jonbro/aleatorium/Firmware/GrooveBox.h

#ifndef GROOVEBOX_H_
#define GROOVEBOX_H_

#include <stdio.h>
#include "pico/stdlib.h"
#include "pico/time.h"
#include "pico/rand.h"

#include "Instrument.h"
extern "C" {
  #include "ssd1306.h"
}
#include "q15.h"
#include "Midi.h"
#include "hardware.h"
#include "voice_data.h"
#include "SongData.h"
#include "audio/resources.h"
#include "Reverb2.h"
#include "Delay.h"
#include "MidiParamMapper.h"
#include "GlobalData.pb.h"
#include "USBSerialDevice.h"
#include "lua.hpp"

#define VOICE_COUNT 8

class GrooveBox {
 public:
  void init(uint32_t *_color, lua_State *L);
  void OnAdcUpdate(uint16_t a);
  void SetGlobalParameter(uint8_t a, uint8_t b, bool setA, bool setB);
  bool IsPlaying();
  int GetNote();
  int GetNoteMidi();
  void Render(int16_t* output_buffer, int16_t* input_buffer, size_t size);
  uint8_t GetInstrumentParamA(int voice);
  uint8_t GetInstrumentParamB(int voice);
  void OnFinishRecording();
  Instrument instruments[VOICE_COUNT];
  int CurrentStep = 0;
  uint8_t currentVoice = 0;
  bool recording = false;
  uint32_t recordingLength;
  bool erasing = false;
  bool playThroughEnabled = false;
  uint8_t GetCurrentPattern()
  {
    return playingPattern;//patternChain[chainStep];
  }

  void ResetADCLatch()
  {
    paramSetA = paramSetB = false;
  }

  void ResetPatternOffset()
  {
    for (size_t i = 0; i < 17; i++)
    {
        patternStep[i] = 0;
        beatCounter[i] = 0;
        if(i<16)
          patternLoopCount[i] = 0;
    }
    beatCounter[17] = 0;
  }
  void OnCCChanged(uint8_t cc, uint8_t newValue);
  static int getTickCountForRateIndex(int rate)
  {
    switch(rate)
    {
      case 0: // 2x
        return 12;
      case 1: // 3/2x
        return 16;
        break;
      case 2: // 1x
        return 24;
        break;
      case 3: // 3/4x
        return 32;
        break;
      case 4: // 1/2x
        return 48;
        break;
      case 5: // 1/4x
        return 96;
        break;
      case 6: // 1/8x
        return 192;
        break;
      case 7: // 24ppq
        return 4;
    }
    return 24;
  }
  VoiceData patterns[16];
  void StartPlaying();
  int syncsRequired = 0;
  uint8_t globalVolume = 0x0;

 private:
  lua_State *L;
  void SaveAndShutdown();
  USBSerialDevice *usbSerialDevice;
  MidiParamMapper midiMap;
  int8_t needsInitialADC = 30; 
  void SerializeToSerial();
  void DeserializeFromSerial();
  void TriggerInstrument(uint8_t key, int16_t midi_note, uint8_t step, uint8_t pattern, bool livePlay, VoiceData &voiceData, int channel);
  void TriggerInstrumentMidi(int16_t midi_note, uint8_t step, uint8_t pattern, VoiceData &voiceData, int channel);
  void CalculateTempoIncrement();
  void OnTempoPulse();
  uint8_t voiceCounter = 0;
  uint8_t instrumentParamA[8];
  uint8_t instrumentParamB[8];
  int needsNoteTrigger = -1;
  int drawY = 0;
  uint16_t drawCount = 0;
  int lastNotePlayed = 60;
  uint8_t lastKeyPlayed = 0;
  bool paramSetA, paramSetB;
  uint32_t tempoPhaseIncrement = 0, tempoPhase = 0;
  uint8_t beatCounter[20] = {0};
  bool playing = false;
  bool waitingForSync = false;
  bool writing = false;
  bool holdingWrite = false;
  bool holdingEscape = false;
  bool holdingMute = false;
  bool holdingArm = false;
  uint8_t recordingTarget = 0;
  int clearTime = -1;
  int shutdownTime = -1;
  int powerHoldTime = -1;
  bool liveWrite = false;
  bool soundSelectMode = false;
  bool patternSelectMode = false;
  bool paramSelectMode = false;
  
  // used for midi learn mode
  int16_t lastEditedParam = -1;
  
  bool selectedGlobalParam = false;
  uint8_t param = 5;
  uint32_t *color;
  uint16_t hadTrigger = 0;
  // defaults to allow all playback
  uint16_t allowPlayback = 0xffff;
  // each sound can be on a different step through the pattern, we should track these
  uint8_t patternStep[17] = {0};

  // for tracking how many times we've looped through a pattern
  uint8_t patternLoopCount[16] = {0};

  uint32_t framesSinceLastTouch = 0;
  // the page we are currently editing for each sound
  // clamped to the length of this pattern / sound
  uint8_t editPage[16] = {0};
  uint8_t playingPattern = 0;
  int patternChain[16] = {0};
  int8_t voiceChannel[16] = {-1};
  
  int patternChainLength = 1;
  int chainStep = 0;
  bool nextPatternSelected = false;
  uint8_t storingParamLockForStep = 0;
  bool parameterLocked;
  VoiceData *Editing;
  VoiceData *Playing;
  SongData songData;
  Midi midi;
  uint16_t nextTrigger = 0;
  uint8_t lastAdcValA = 0;
  uint8_t lastAdcValB = 0;
  uint16_t AdcInterpolatedA = 0;
  uint16_t AdcInterpolatedB = 0;
  Delay delay;
  Reverb2 verb;
  int64_t renderTime = 0;
  int64_t sampleCount = 0;
  GlobalData globalData = GlobalData_init_zero;
};

extern GrooveBox *groovebox; // used for the midi callbacks

#endif // GROOVEBOX_H_
