jonbro/aleatorium/Firmware/Midi.cc

#include "Midi.h"
#include "hardware/irq.h"
#include "hardware/dma.h"
#include <stdio.h>
#include <string.h>
#include "tusb.h"

#define UART_ID uart1
#define BAUD_RATE 31250
#define UART_TX_PIN 4
#define UART_RX_PIN 5

static int chars_rxed = 0;
uint8_t in_buf[128];
uint8_t buf_count = 0;
bool readBuf = false;
void on_uart_rx() {
    while (uart_is_readable(UART_ID)) {
        char c = uart_getc(UART_ID);
        in_buf[buf_count++] = c;
        readBuf = false;
    }
}

void Midi::Init()
{
    // clear out the last values so we immediately update on first get
    for(int i=0;i<128;i++)
    {
        lastCCValue[i] = 0xff;
    }
    // Set up our UART with the required speed.
    uart_init(UART_ID, BAUD_RATE);

    // Set the TX and RX pins by using the function select on the GPIO
    // Set datasheet for more information on function select
    gpio_set_function(UART_TX_PIN, GPIO_FUNC_UART);
    gpio_set_function(UART_RX_PIN, GPIO_FUNC_UART);

    int UART_IRQ = UART_ID == uart0 ? UART0_IRQ : UART1_IRQ;
    irq_set_exclusive_handler(UART_IRQ, on_uart_rx);
    irq_set_enabled(UART_IRQ, true);

    // Now enable the UART to send interrupts - RX only
    uart_set_irq_enables(UART_ID, true, false);
    TxIndex = 0;
    //
    DmaChannelTX = dma_claim_unused_channel(true);

    dma_channel_config txConfig = dma_channel_get_default_config(DmaChannelTX);
    channel_config_set_transfer_data_size(&txConfig, DMA_SIZE_8);
    channel_config_set_read_increment(&txConfig, true);
    channel_config_set_write_increment(&txConfig, false);
    channel_config_set_ring(&txConfig, false, MIDI_BUF_LENGTH_POW);
    channel_config_set_dreq(&txConfig, DREQ_UART1_TX);
    dma_channel_set_config(DmaChannelTX, &txConfig, false);
    dma_channel_set_write_addr(DmaChannelTX, &uart1_hw->dr, false);
    initialized = true;
}

uint16_t Midi::Write(const uint8_t* data, uint16_t length)
{
}

void Midi::Flush()
{
    if(!initialized || dma_channel_is_busy(DmaChannelTX))
        return;
    // Size check
    if (TxIndex == 0)
    {
        return;
    }
    uint8_t* start = &TxBuffer[MIDI_BUF_LENGTH*pingPong];
    dma_channel_transfer_from_buffer_now(DmaChannelTX, start, TxIndex);
    pingPong = (pingPong+1)%2;
    TxIndex = 0;
}

int Midi::GetNote()
{
    if(readBuf)
        return -1;

    uint8_t cmdStart = 0;
    // filter out all non 0x9 commands
    while(((in_buf[cmdStart]>>4) != 0x9 && (in_buf[cmdStart]>>4) != 0xb) && cmdStart<buf_count)
    {
        cmdStart++;
        while((in_buf[cmdStart]>>7) != 1 && cmdStart<buf_count)
        {
            cmdStart++;
        }
    }
    if(cmdStart>buf_count)
    {
        buf_count = 0;
        return -1;
    }
    if((in_buf[cmdStart]>>4) == 0x9)
    {
        readBuf = true;
        buf_count = 0;
        return in_buf[cmdStart+1]&0x7f; // midi data bytes strip off the top bit
    }
    // control change
    if((in_buf[cmdStart]>>4) == 0xb)
    {
        uint8_t cc = in_buf[cmdStart+1];
        uint8_t val = in_buf[cmdStart+2];
        if(lastCCValue[cc] == 0xff || lastCCValue[cc] != val)
        {
            if(OnCCChanged != NULL)
            {
                OnCCChanged(cc, val);
            }
            lastCCValue[cc] = val;
        }
        //printf("cc: %i %i\n",in_buf[cmdStart+1], in_buf[cmdStart+2]);
        buf_count = 0;
        return -1;
    }
    // note off
    buf_count = 0;
    return -1;
}
void Midi::NoteOn(uint8_t channel, uint8_t pitch, uint8_t velocity)
{
    uint8_t send[] = {0x90+channel,pitch,velocity};
    Write(send, 3);
}

void Midi::NoteOff(uint8_t channel, uint8_t pitch)
{
    uint8_t send[] = {0x90+channel,pitch,0};
    Write(send, 3);
}

void Midi::StartSequence()
{
    uint8_t sendValue = 0xFA;
    Write(&sendValue, 1);
}
void Midi::StopSequence()
{
    uint8_t sendValue = 0xFC;
    Write(&sendValue, 1);
}
void Midi::TimingClock()
{
    uint8_t sendValue = 0xF8;
    Write(&sendValue, 1);
}
