jonbro/aleatorium/Firmware/AudioSampleSecondbloop.cpp

// Audio data converted from WAV file by wav2sketch

#include "AudioSampleSecondbloop.h"

// Converted from secondbloop.wav, using 44100 Hz, 16 bit PCM encoding
const unsigned int AudioSampleSecondbloop[16065] = {
0x81007D03,0x089B006F,0x1A1111C8,0x2AB322D2,0x3A0D32D2,0x47A8414E,0x531F4DDA,0x5C195811,
0x62545FAA,0x65A0646B,0x65E7662A,0x632164E3,0x5D69609B,0x54EA5975,0x49E44FA2,0x3CA84379,
0x2DA1354F,0x1D44258D,0x0C0914AE,0xFA710336,0xE906F1AA,0xD84DE08C,0xC8C3D061,0xBAE6C1A0,
0xAF19B4BB,0xA5B4AA14,0x9F01A1FF,0x9B2C9CBC,0x9A599A6E,0x9C959B25,0xA1C59ED3,0xA9C0A56D,
0xB447AEB9,0xC113BA6F,0xCFBAC835,0xDFD3D7A2,0xF0DDE83E,0x0256F990,0x13BB0B14,0x248A1C3C,
0x343C2C8D,0x425B3B90,0x4E8748C2,0x586153C5,0x5F905C46,0x63E3620E,0x653964EF,0x639364CA,
0x5EFA619E,0x57845B91,0x4D7752CB,0x411F4790,0x32D83A31,0x230F2B1B,0x123D1ABD,0x00E40996,
0xEF87F826,0xDEAAE6F3,0xCEC8D685,0xC05EC757,0xB3DDB9DE,0xA9A3AE76,0xA201A57E,0x9D2C9F35,
0x9B459BD0,0x9C599B6D,0xA0639E0C,0xA74FA390,0xB0E2ABCC,0xBCCAB688,0xCAAAC37A,0xDA1FD23B,
0xEAB4E256,0xFBEDF34D,0x0D4504A0,0x1E3315CE,0x2E382655,0x3CD735B8,0x49A74381,0x54454F43,
0x5C6158A6,0x61BC5F64,0x6429634C,0x639D6440,0x60196237,0x59B75D43,0x50AC558B,0x453F4B42,
0x37C33EBD,0x289D305E,0x18462091,0x07380FC9,0xF5F5FE90,0xE4FBED64,0xD4D5DCCB,0xC5FECD3B,
0xB8E1BF2E,0xADDDB319,0xA553A94D,0x9F81A211,0x9C8B9DA4,0x9C899C27,0x9F7C9DA5,0xA54FA212,
0xADD9A945,0xB8D1B30C,0xC5E5BF1F,0xD4B3CD1E,0xE4CBDC9E,0xF5AFED29,0x06DCFE43,0x17D30F6B,
0x28162019,0x37232FCD,0x448A3E16,0x4FE64A84,0x58DF54B6,0x5F335C62,0x62AE614E,0x633C6352,
0x60D46262,0x5B895E83,0x538657D7,0x49064E8E,0x3C5B42F1,0x2DEB3553,0x1E1C2621,0x0D6815CF,
0xFC4C04DE,0xEB50F3CA,0xDAF6E314,0xCBBED33A,0xBE19C4B0,0xB269B7ED,0xA902AD58,0xA236A53D,
0x9E369FD2,0x9D1A9D4B,0x9EF29DB5,0xA3B6A107,0xAB38A726,0xB53DAFED,0xC177BB18,0xCF8BC84E,
0xDF0ED731,0xEF91E740,0x008EF808,0x117E090F,0x21E819D3,0x315329C9,0x3F403880,0x4B474588,
0x5512507E,0x5C545909,0x60D75EEC,0x627361FC,0x61196227,0x5CE05F69,0x55E959CF,0x4C695181,
0x40A346C7,0x32EC39F8,0x23AF2B74,0x136C1BA7,0x02950B03,0xF1A9FA12,0xE129E956,0xD1A0D943,
0xC378CA57,0xB71FBD06,0xACF4B1B7,0xA543A8BB,0xA045A25C,0x9E1D9ECA,0x9EE09E1F,0xA290A05A,
0xA901A569,0xB200AD35,0xBD55B779,0xCAB1C3D8,0xD99ED1FC,0xE9A3E185,0xFA56F1F8,0x0B3402CD,
0x1BB6138D,0x2B6323B8,0x39C732CE,0x466F405E,0x50FE4C01,0x59215560,0x5E9B5C35,0x61416049,
0x61066182,0x5DE65FCE,0x57F65B46,0x4F6A5409,0x44894A47,0x37A03E4C,0x2908307C,0x193D2140,
0x08B71106,0xF7EE0048,0xE762EF91,0xD795DF5B,0xC904D019,0xBC16C245,0xB12AB64E,0xA897AC8E,
0xA2A0A54A,0x9F74A0BA,0x9F2A9EFD,0xA1C7A021,0xA72FA41E,0xAF36AAD9,0xB9A5B422,0xC627BFA9,
0xD464CD1B,0xE3EBDC0D,0xF44DEC0A,0x0500FC9E,0x15890D4D,0x256D1D94,0x34362CF6,0x416B3AFC,
0x4CA74746,0x559C5170,0x5C095927,0x5FB45E34,0x60846076,0x5E705FDB,0x59935C66,0x520F562A,
0x48164D5F,0x3BFA424D,0x2E18353F,0x1ED8269D,0x0EAD16D9,0xFE13066A,0xED8BF5CD,0xDD94E57E,
0xCEA7D5FA,0xC132C7B7,0xB59CBB26,0xAC3FB0A5,0xA561A87F,0xA138A2F8,0x9FE5A032,0xA16BA046,
0xA5BDA33B,0xACBEA8F2,0xB642B13E,0xC1F9BBD7,0xCF80C87A,0xDE71D6CA,0xEE61E655,0xFEDAF69C,
0x0F5D0726,0x1F661774,0x2E7F2712,0x3C313580,0x4812425B,0x51D14D3B,0x592255C6,0x5DC65BC5,
0x5F9E5F0A,0x5EA05F7B,0x5ACF5D11,0x544A57E6,0x4B47501C,0x400E45EA,0x32E239A6,0x24342BB9,
0x14731C7B,0x04210C66,0xF3B3FBEE,0xE3A1EB98,0xD469DBE4,0xC67CCD46,0xBA4AC02E,0xB031B4F9,
0xA876AC01,0xA356A58E,0xA0F7A1CF,0xA173A0DB,0xA4BEA2B9,0xAABBA762,0xB344AEB0,0xBE16B862,
0xCAD5C43C,0xD92CD1DD,0xE8B2E0D3,0xF8E4F0B1,0x09410109,0x1955115E,0x28AD2125,0x36CA2FED,
0x43423D46,0x4DBA48CE,0x55E55222,0x5B7B5903,0x5E555D43,0x5E5E5EBD,0x5B9C5D63,0x5624593E,
0x4E1C526E,0x43C0492E,0x37613DC3,0x295C3080,0x1A1B21D5,0x0A171227,0xF9CA01F0,0xE9ACF1AD,
0xDA3DE1DA,0xCBEDD2ED,0xBF2BC55E,0xB45EB98D,0xABD8AFD0,0xA5CFA877,0xA274A3C0,0xA1DEA1CC,
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
};
